ADA-EC/SEMEADA/Testes Arduino/MostrarUmaImagem/aberto.bmp

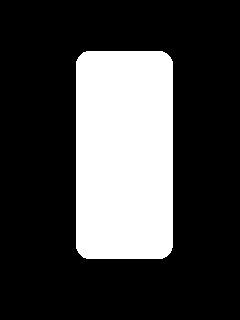
Testes Arduino/MostrarUmaImagem/aberto.bmp
