ADA-EC/SEMEADA/Testes Arduino/robot_vector/feliz.bmp

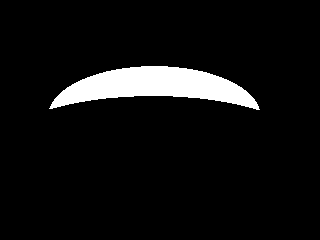
Testes Arduino/robot_vector/feliz.bmp
