ADA-EC/SEMEADA/Testes Arduino/robot_vector/raiva_esq.bmp

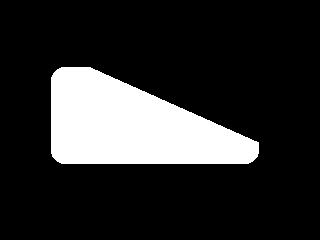
Testes Arduino/robot_vector/raiva_esq.bmp
