ADA-EC/SEMEADA/Testes Arduino/robot_vector/eyes.h

//Sobrancelha
static const unsigned char PROGMEM eye0[] =
{ 
  B00000000,B00000000,B00000000,B00000000,
  B00000000,B00000000,B00000000,B00000000,
  B00000000,B00000000,B00000000,B00000000,
  B00000000,B00000000,B00000000,B00000000,
  B00000000,B00000000,B00000000,B00000000,
  B00000000,B00000000,B00000000,B00000000,
  B00000000,B00000000,B00000000,B00000000,
  B00000000,B00000000,B00000000,B00000000,
  B00000000,B00000000,B00000000,B00000000,
  B00000000,B00000000,B00000000,B00000000,
  B00000000,B00000000,B00000000,B00000000,
  B00000000,B00000000,B00000000,B00000000,
  B00000000,B00000000,B00000000,B00000000,
  B00000000,B00000000,B00000000,B00000000,
  B00000000,B00000000,B00000000,B00000000,
  B00000000,B00000000,B00000000,B00000000,
  B00000000,B00000000,B00000000,B00000000,
  B11111111,B11111111,B11111111,B11111111,
  B11111111,B11111111,B11111111,B11111111,
  B11111111,B11111111,B11111111,B11111111,
  B11111111,B11111111,B11111111,B11111111,
  B00000000,B00000000,B00000000,B00000000,
  B00000000,B00000000,B00000000,B00000000,
  B00000000,B00000000,B00000000,B00000000,
  B00000000,B00000000,B00000000,B00000000,
  B00000000,B00000000,B00000000,B00000000,
  B00000000,B00000000,B00000000,B00000000,
  B00000000,B00000000,B00000000,B00000000,
  B00000000,B00000000,B00000000,B00000000,
  B00000000,B00000000,B00000000,B00000000,
  B00000000,B00000000,B00000000,B00000000,
  B00000000,B00000000,B00000000,B00000000,
};

// Olho aberto
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
	0x00, 0x00, 0x00, 0x00, 0x00, 0x00, 0x00, 0x00, 0x00, 0x00, 0x00, 0x00, 0x00, 0x00, 0x00, 0x00, 
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
};



// [mood][pos][l/r]
const unsigned char *peyes[][3][2]={
 { {epd_bitmap_aberto, epd_bitmap_aberto},{epd_bitmap_aberto, epd_bitmap_aberto},{epd_bitmap_aberto, epd_bitmap_aberto} }
};
